suprcrackers/NESRGB-IGR/NES-IO/pictures/Frontpanel.jpg

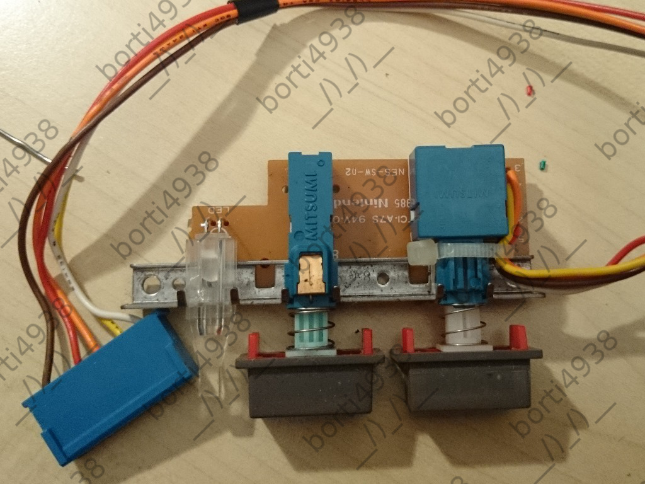
NES-IO/pictures/Frontpanel.jpg
