suprcrackers/NESRGB-IGR/NES-IO/pictures/GC_Buchse_Empfehlung.jpg

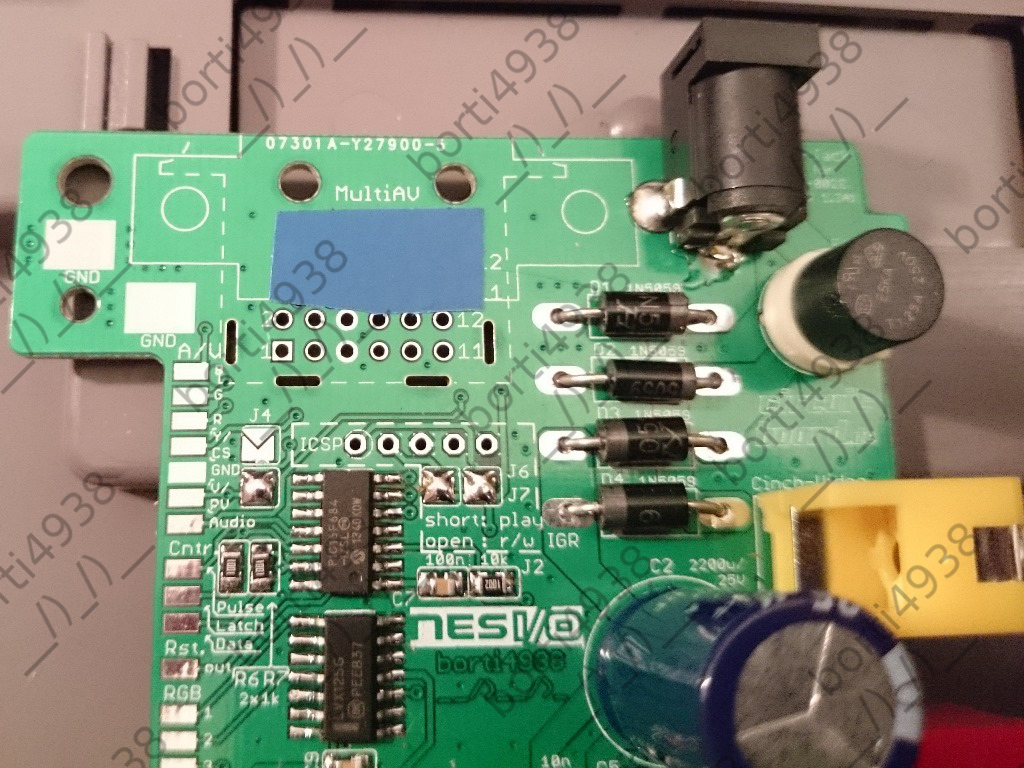
NES-IO/pictures/GC_Buchse_Empfehlung.jpg
