suprcrackers/NESRGB-IGR/NES-IO/pictures/NES-IO.jpg

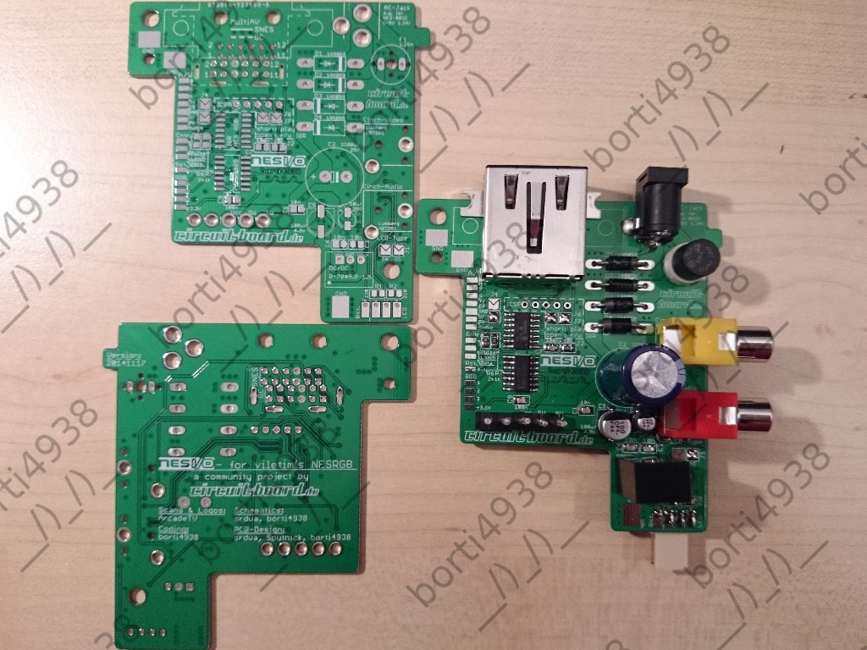
NES-IO/pictures/NES-IO.jpg
