suprcrackers/NESRGB-IGR/NES-IO/pictures/NESRGB_123.jpg

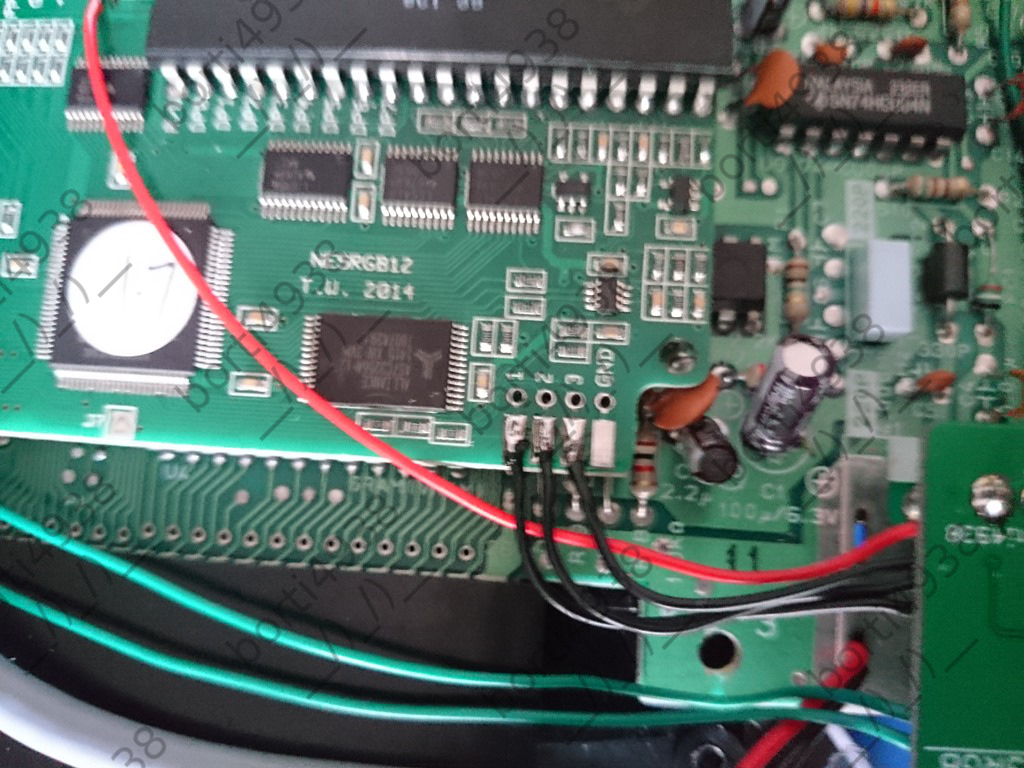
NES-IO/pictures/NESRGB_123.jpg
