suprcrackers/NESRGB-IGR/NES-IO/pictures/Platinenhochzeit.jpg

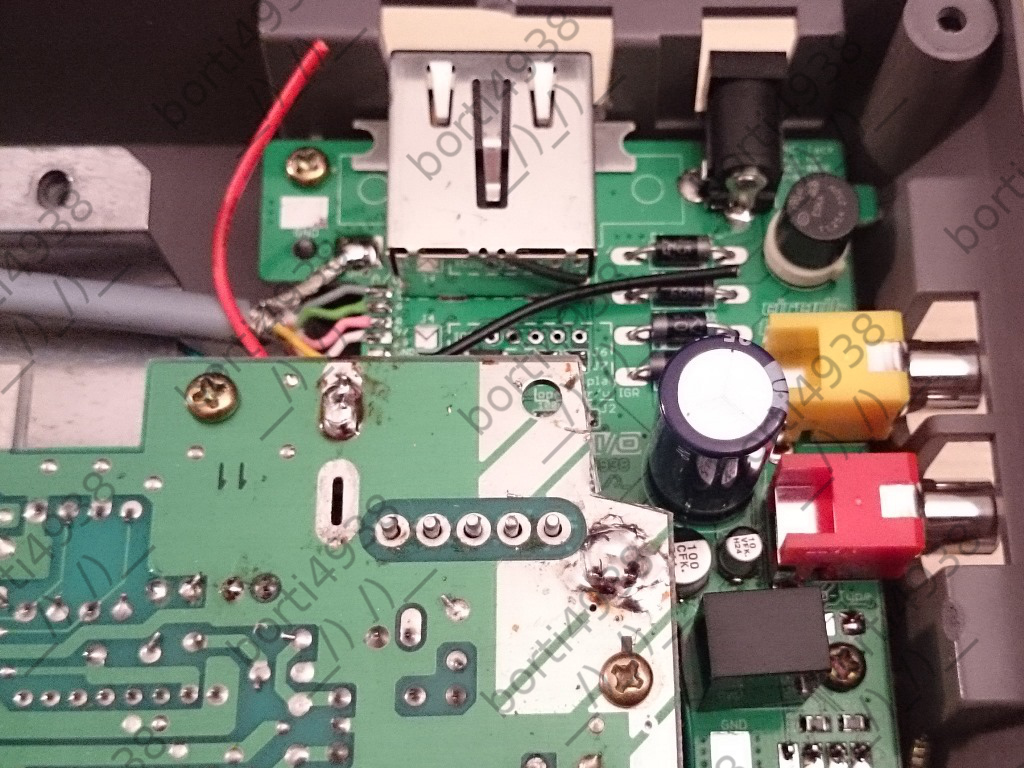
NES-IO/pictures/Platinenhochzeit.jpg
