suprcrackers/NESRGB-IGR/NES-IO/pictures/Ready.jpg

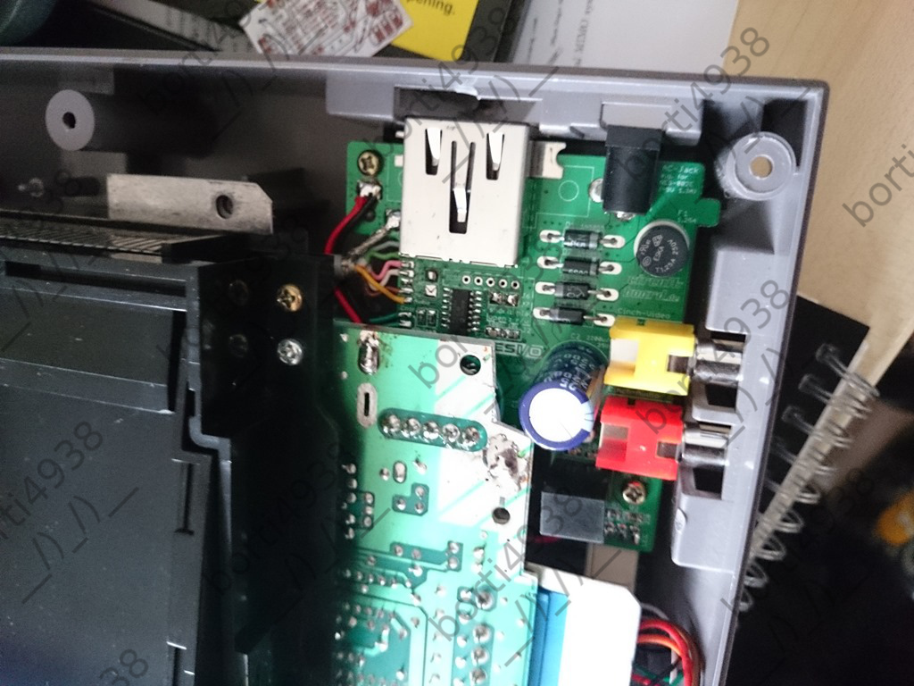
NES-IO/pictures/Ready.jpg
