suprcrackers/NESRGB-IGR/NES-IO/pictures/SNES-Buchse.jpg

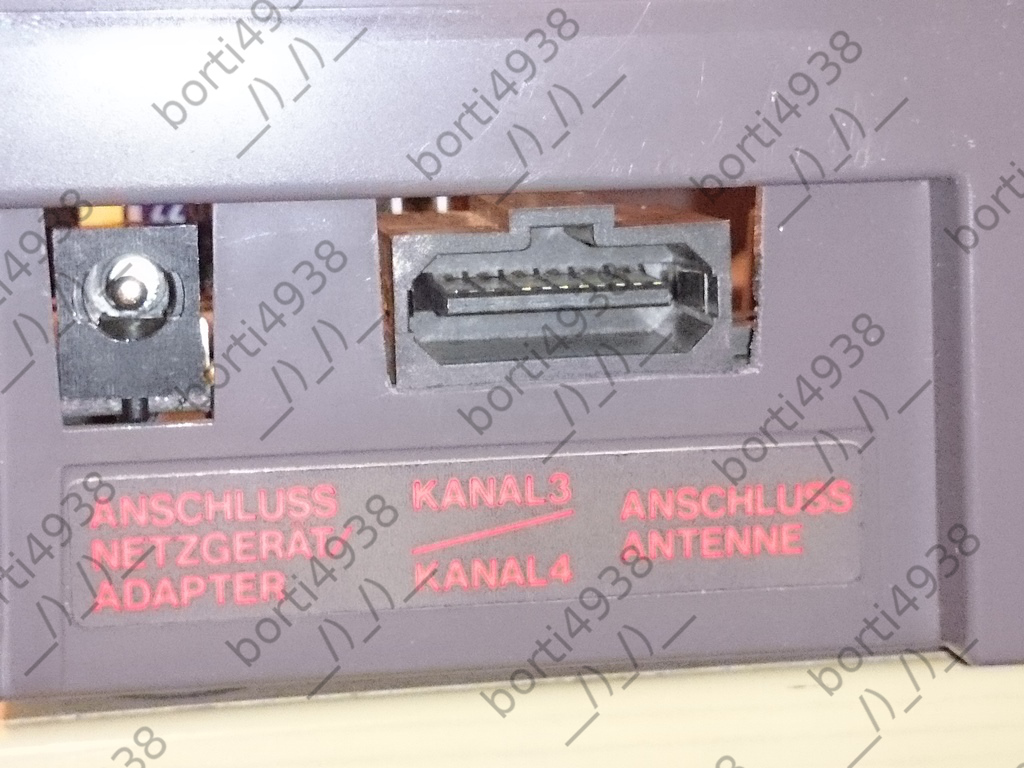
NES-IO/pictures/SNES-Buchse.jpg
