suprcrackers/NESRGB-IGR/Normal-Version/Installation/RGB_123.jpg

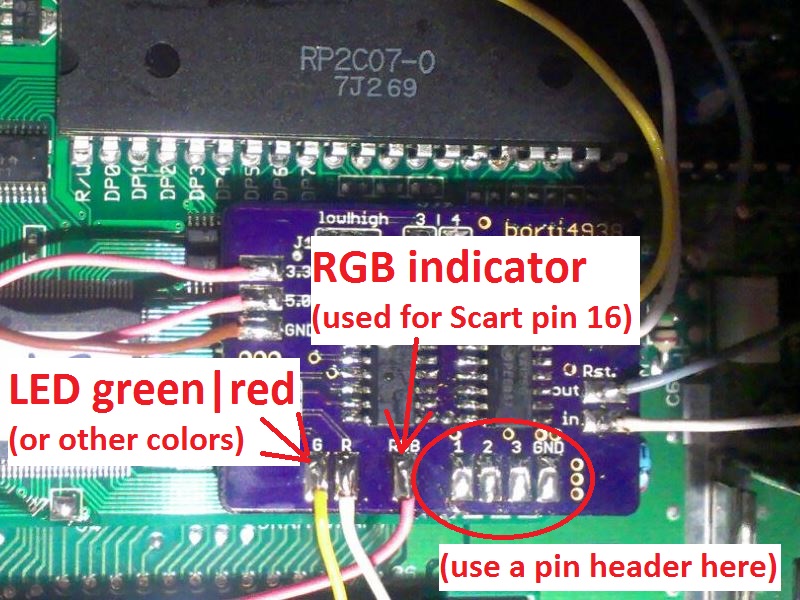
Normal-Version/Installation/RGB_123.jpg
